hanneslinder/retro-speaker/images/20220124_123417.jpg

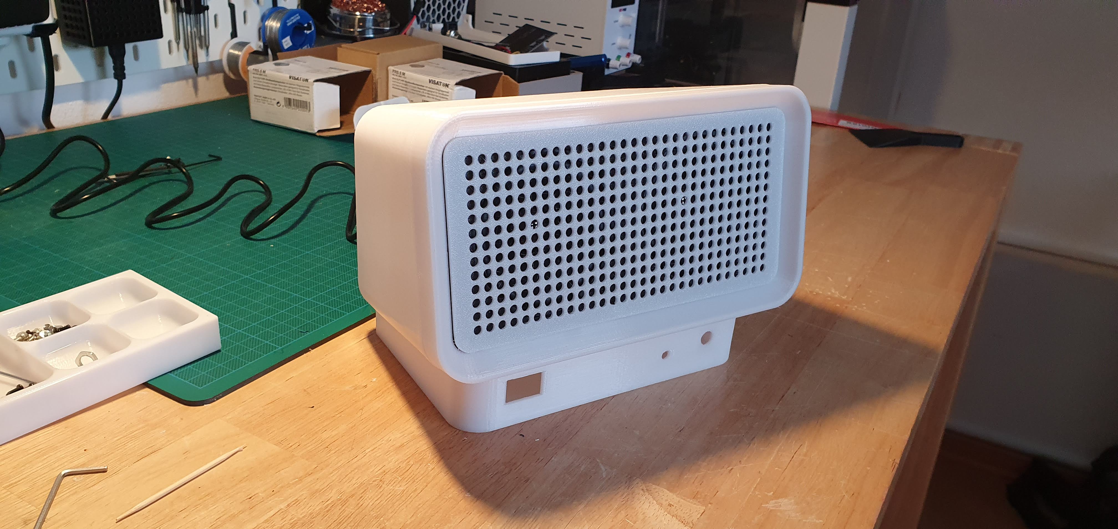
images/20220124_123417.jpg
