hanneslinder/retro-speaker/images/20220130_214704.jpg

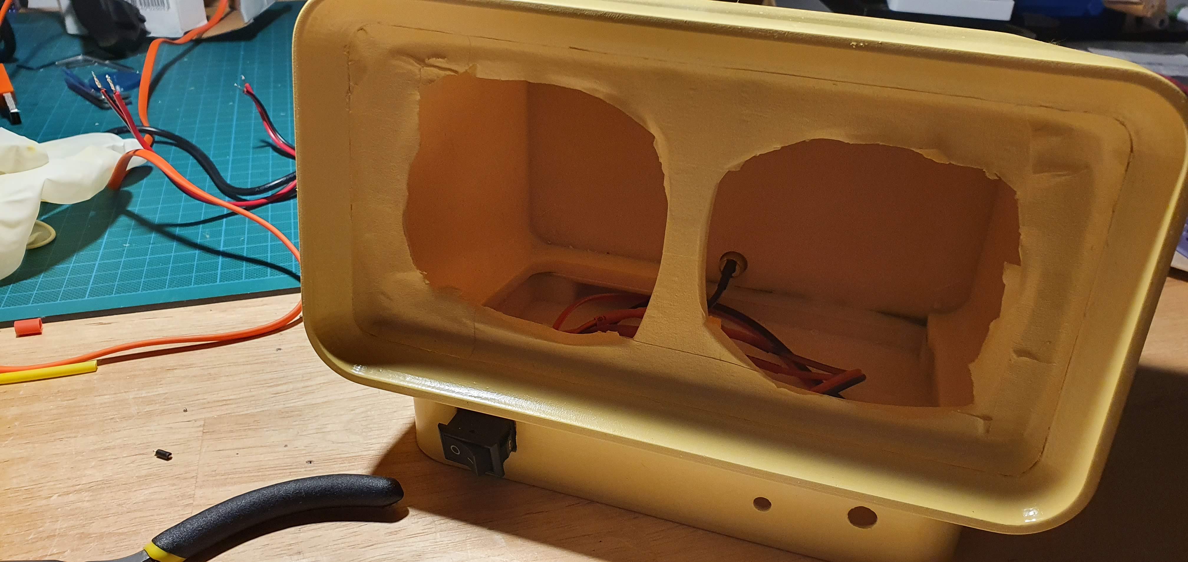
images/20220130_214704.jpg
