hanneslinder/retro-speaker/images/20220131_142246.jpg

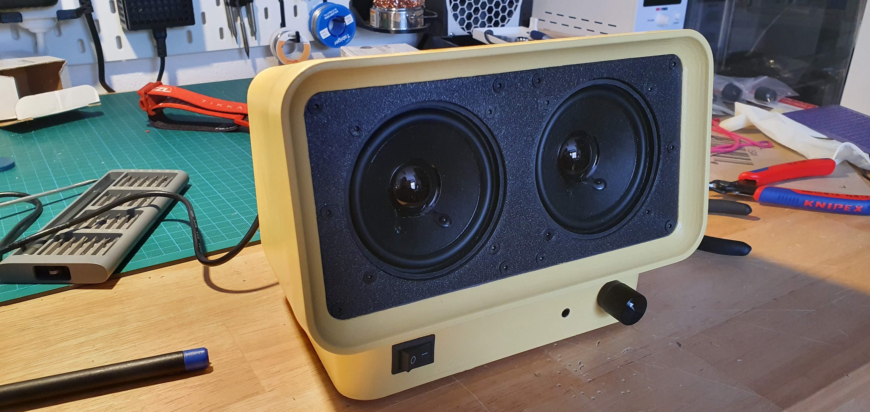
images/20220131_142246.jpg
